focusaurus/kipra-keyboard/v1/case/case-prototype-5.FCStd

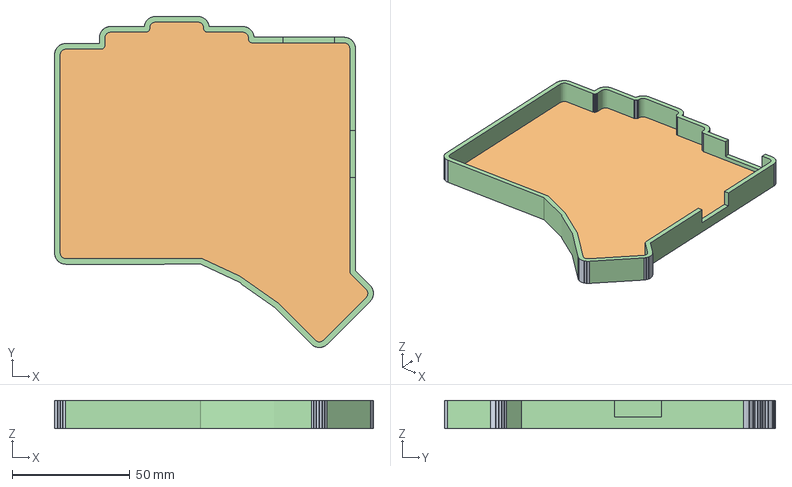
[picture p19: CAD file, 2024-05-14, an earlier design]
v1/case/case-prototype-5.FCStd
135.2 x 140.4 x 12.0 mm
Cutout001
Extrude001 (Meshed)
Cutout001 (Meshed)
