focusaurus/kipra-keyboard/v1/case/case-clip.FCStd

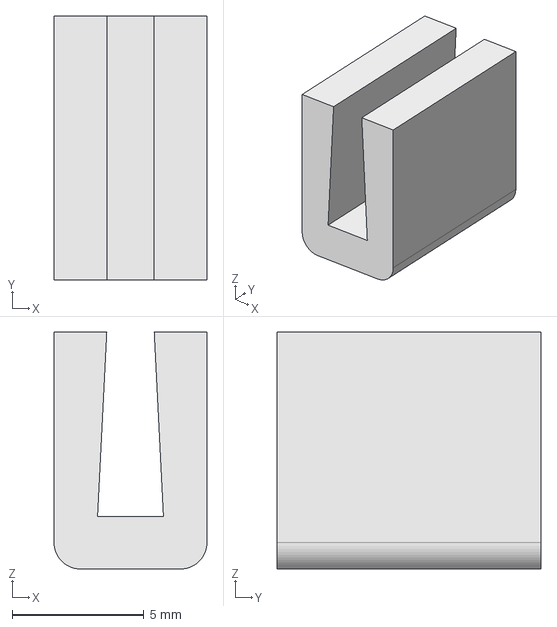
[picture p20: CAD file, 2024-05-14, an earlier design]
v1/case/case-clip.FCStd
5.80 x 10.0 x 8.99 mm
