focusaurus/kipra-keyboard/v1/case/case-prototype-4.FCStd

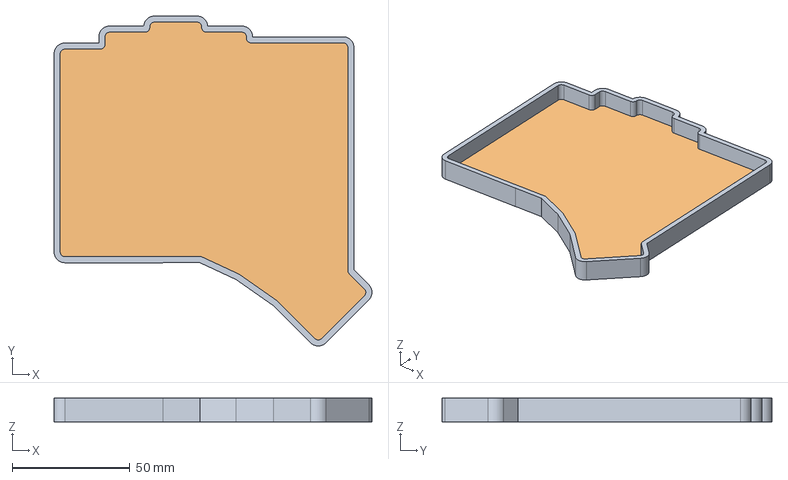
[picture p21: CAD file, 2024-05-14, an earlier design]
v1/case/case-prototype-4.FCStd
134.8 x 140.0 x 10.0 mm
BaseFeature
